anvaymathur/CustomKeyboard-1/Assets/AddingGPIOExtender.png

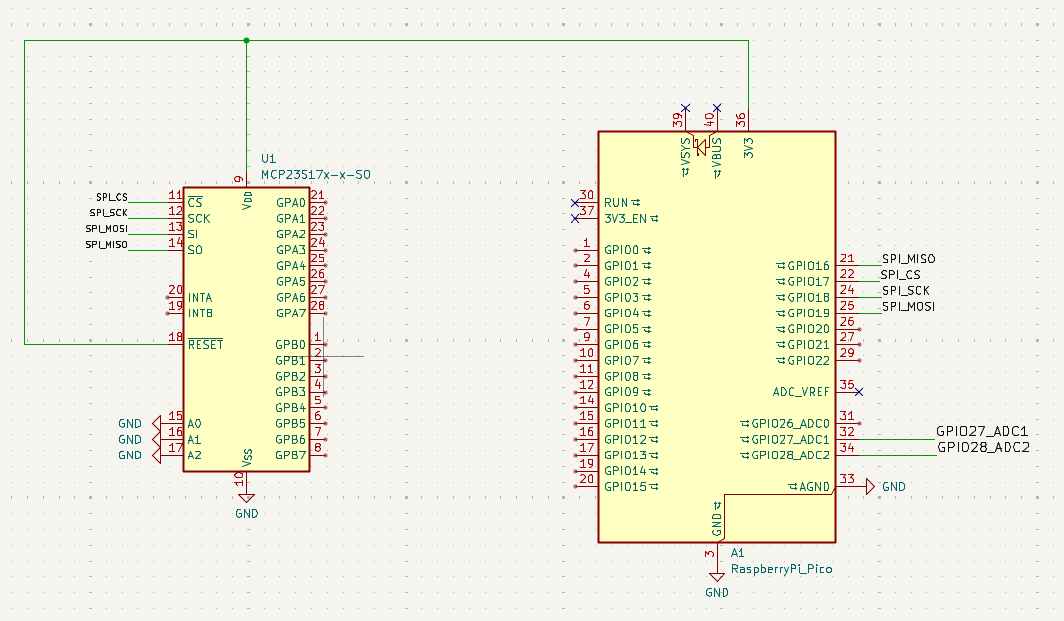
Assets/AddingGPIOExtender.png
