anvaymathur/CustomKeyboard-1/Assets/FullCase.png

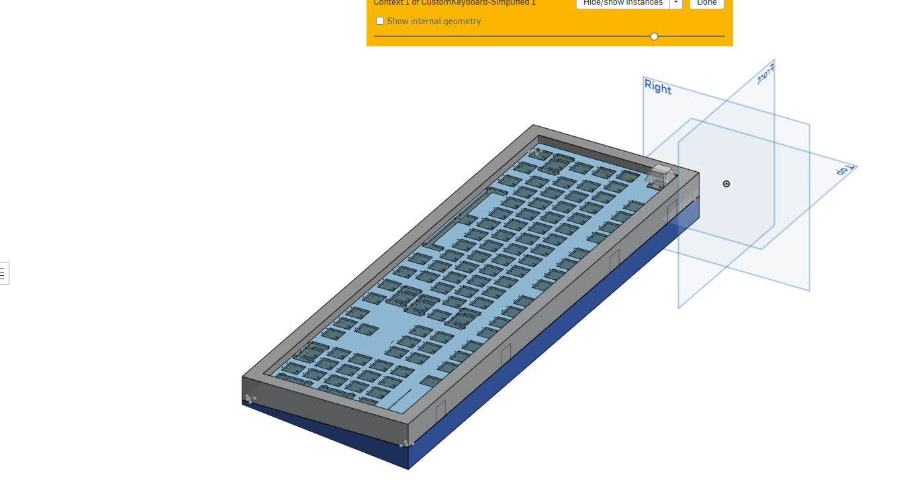
Assets/FullCase.png
