anvaymathur/CustomKeyboard-1/Assets/MountType.png

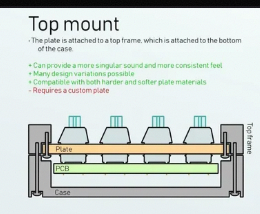
Assets/MountType.png
