anvaymathur/CustomKeyboard-1/Assets/Potential Keyboard Layout.png

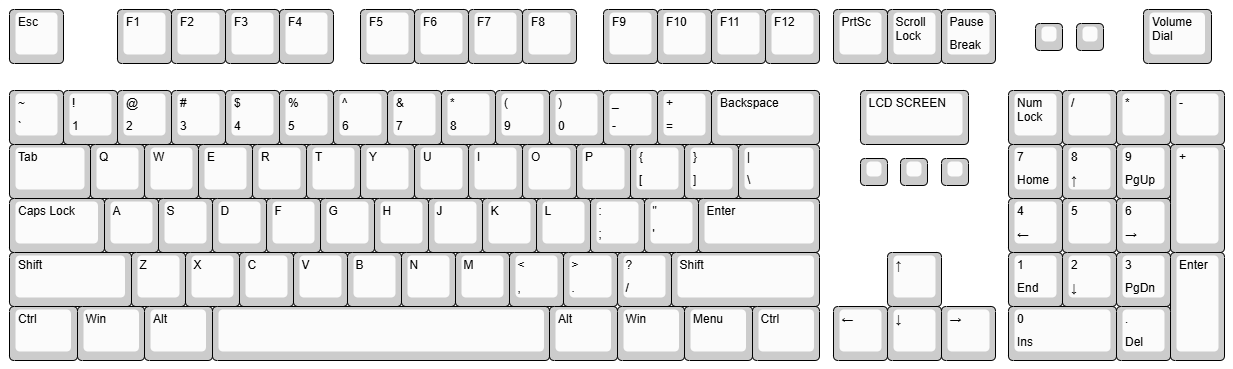
Assets/Potential Keyboard Layout.png
